turingbirds/ping-clock/esp32-firmware/src/gamma.h

// Gramma Correction (Defalt Gamma = 2.8)
const uint8_t gammaR[] = {
  0,   0,   0,   0,   0,   0,   0,   0,   0,   0,   0,   0,   0,
        0,   0,   0,   0,   0,   0,   0,   0,   0,   0,   0,   0,   0,
        0,   0,   0,   0,   0,   0,   0,   0,   0,   0,   0,   0,   0,
        0,   0,   0,   0,   0,   0,   0,   0,   0,   0,   0,   0,   1,
        1,   1,   1,   1,   1,   1,   1,   1,   1,   1,   1,   2,   2,
        2,   2,   2,   2,   2,   2,   2,   3,   3,   3,   3,   4,   4,
        4,   4,   4,   4,   5,   5,   5,   5,   5,   5,   6,   6,   6,
        7,   7,   7,   7,   7,   8,   8,   9,   9,  10,  10,  10,  10,
       11,  11,  12,  12,  13,  13,  13,  13,  14,  15,  15,  16,  16,
       16,  17,  17,  18,  19,  19,  19,  20,  20,  21,  22,  22,  23,
       24,  24,  24,  25,  26,  27,  28,  28,  29,  29,  30,  31,  32,
       33,  33,  34,  35,  35,  36,  37,  38,  39,  40,  41,  42,  43,
       44,  44,  45,  46,  47,  48,  50,  51,  52,  53,  54,  55,  56,
       58,  58,  59,  60,  62,  63,  64,  65,  67,  68,  69,  71,  72,
       73,  75,  76,  78,  79,  81,  82,  83,  85,  86,  88,  89,  91,
       93,  94,  96,  98, 100, 101, 103, 105, 106, 108, 110, 112, 113,
      115, 118, 120, 121, 123, 125, 127, 130, 132, 133, 135, 137, 139,
      142, 144, 146, 148, 151, 153, 155, 157, 160, 162, 164, 167, 170,
      172, 174, 177, 179, 182, 185, 187, 189, 193, 195, 197, 201, 203,
      206, 209, 212, 215, 218, 221, 224, 226, 230 };

const uint8_t gammaG[] = {
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
   90, 92, 93, 94, 96, 97, 98,100,101,103,104,106,107,109,110,112,
  113,115,116,118,119,121,122,124,126,127,129,131,132,134,136,137,
  139,141,143,144,146,148,150,152,153,155,157,159,161,163,165,167,
  169,171,173,175,177,179,181,183,185,187,189,191,193,196,198,200 };
